kooliha/Ouroboros_Loop_Station/docs/Ouroboros.png

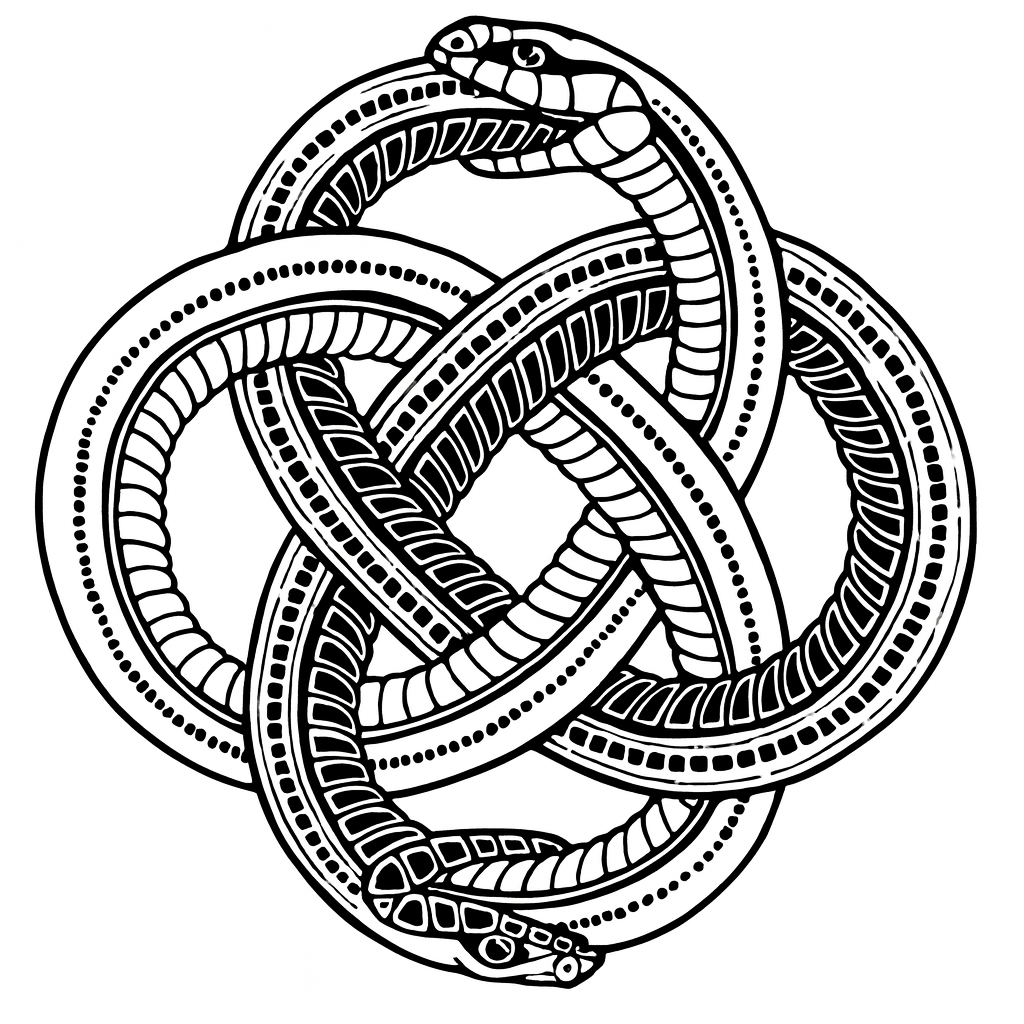
docs/Ouroboros.png
