kooliha/Ouroboros_Loop_Station/Hardware/3d Printing Box 1.1/3D Box.png

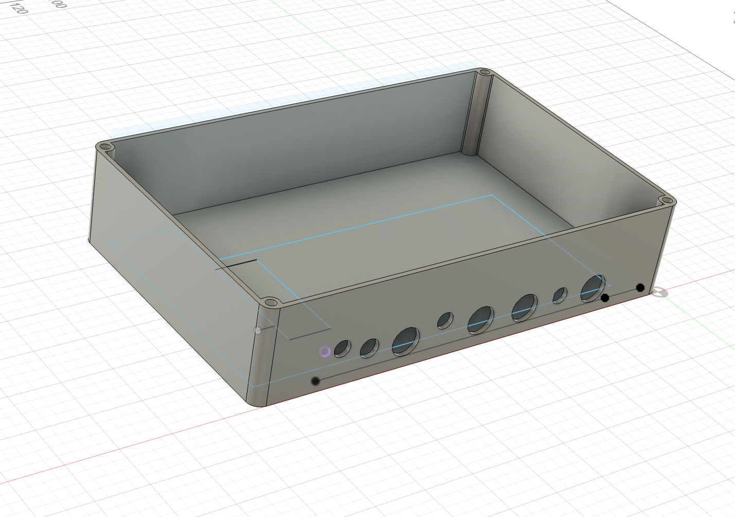
Hardware/3d Printing Box 1.1/3D Box.png
