kooliha/Ouroboros_Loop_Station/Hardware/Photos/PCB Back_Soldered.jpeg

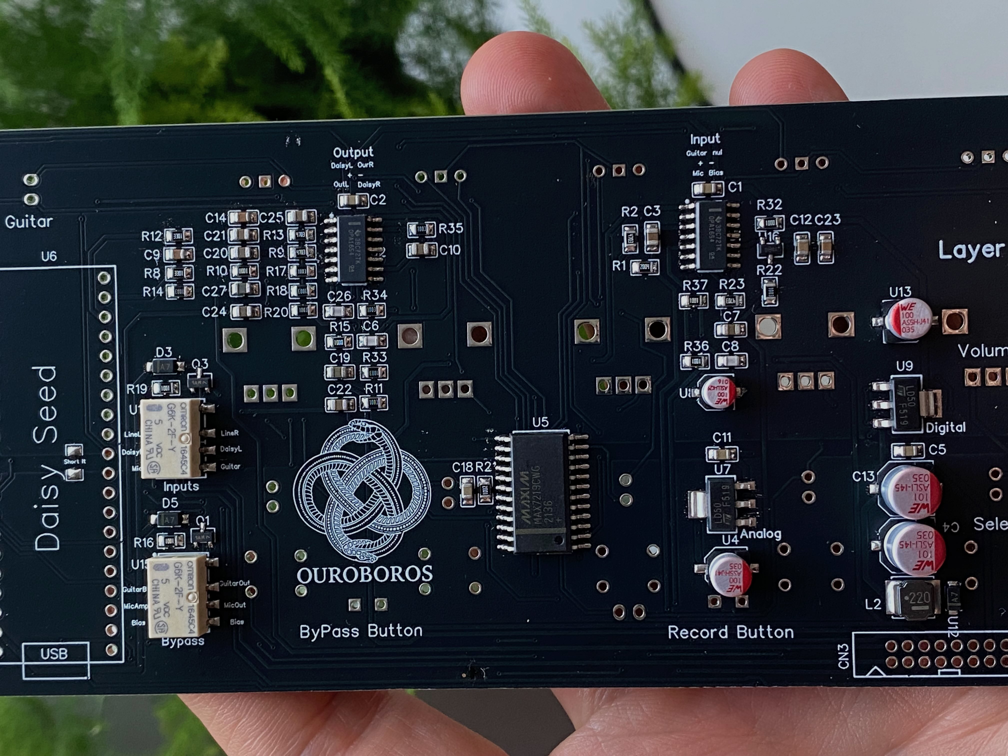
Hardware/Photos/PCB Back_Soldered.jpeg
